impjustme/InkTime/Images/bot.png

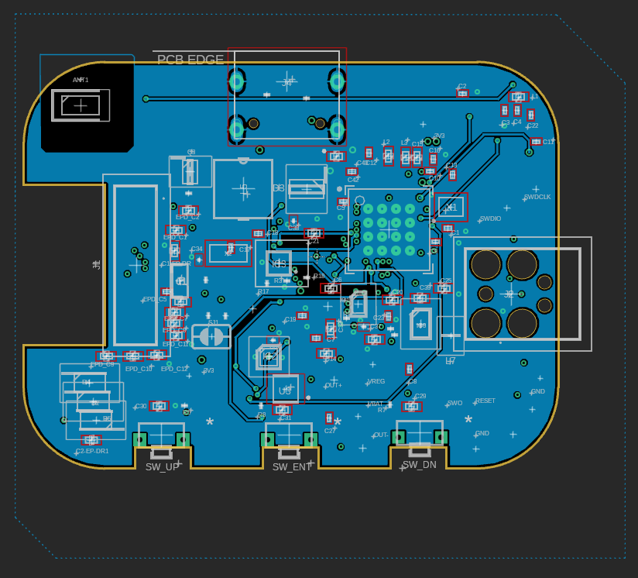
Images/bot.png
