impjustme/InkTime/Images/top_3D.png

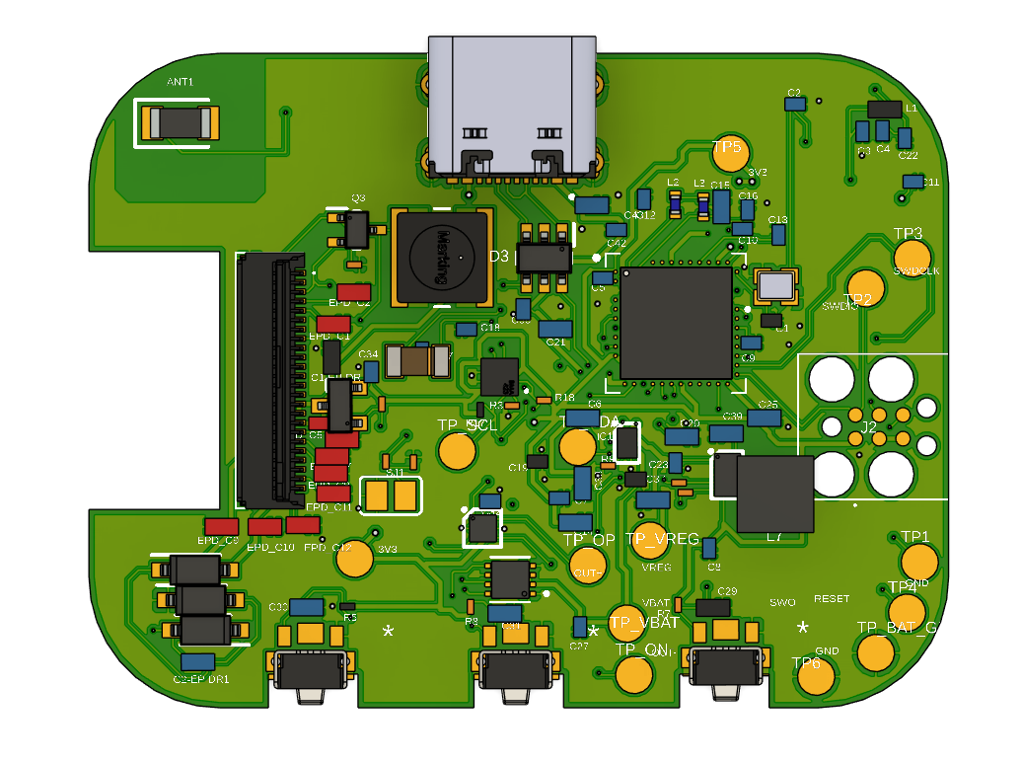
Images/top_3D.png
